GuitarML/SoundSketch/software/Pluto/pluto.cpp

#include "daisy_petal.h"
#include "daisysp.h"
#include "varSpeedLooper.h"
#include "soundsketch.h"
#include "reverbsc96.h"
#include "expressionHandler.h"

//
// This is a template for creating a pedal on the GuitarML Funbox_v1/Daisy Seed platform.
// You can start from here to fill out your effects processing and controls.
// Allows for Stereo In/Out, 6 knobs, 3 3-way switches,  2 SPST Footswitches, 2 LEDs.
//
// Keith Bloemer 5/20/2024
//

using namespace daisy;
using namespace daisysp;
using namespace soundsketch; 

// True bypass
GPIO audioBypassTrigger;
GPIO audioMuteTrigger;
bool m_audioBypass;
bool m_audioMute;

bool muteOn = false;
float muteOffTransitionTimeInSeconds = 0.02f;
int muteOffTransitionTimeInSamples;
int samplesTilMuteOff;

bool bypassOn = false;
float bypassToggleTransitionTimeInSeconds = 0.01f;
int bypassToggleTransitionTimeInSamples;
int samplesTilBypassToggle;


// Declare a local daisy_petal for hardware access
DaisyPetal hw;
Parameter levelA, modA, levelB, speedA, modB, speedB, expression;

// Looper Parameters
#define MAX_SIZE (96000 * 60) // 1 minute of floats at 96 khz
float DSY_SDRAM_BSS bufA[MAX_SIZE];
varSpeedLooper looperA;
Oscillator      led_oscA; // For pulsing the led when recording / paused playback
float           ledBrightnessA;
int             doubleTapCounterA;
bool            checkDoubleTapA;
bool            pausePlaybackA;
float           currentSpeedA;

float DSY_SDRAM_BSS bufB[MAX_SIZE];
varSpeedLooper looperB;
Oscillator      led_oscB; // For pulsing the led when recording / paused playback
float           ledBrightnessB;
int             doubleTapCounterB;
bool            checkDoubleTapB;
bool            pausePlaybackB;
float           currentSpeedB;

bool isPlaybackA, isPlaybackB;

// Reverb
ReverbSc96        verb;  // Minor change to ReverbSc to use 96kHz default samplerate

Tone toneA;       // Low Pass
ATone toneHPA;    // High Pass
Balance balA;     // Balance for volume correction in filtering

Tone toneB;       // Low Pass
ATone toneHPB;    // High Pass
Balance balB;     // Balance for volume correction in filtering

SmoothRandomGenerator smoothRandA;
SmoothRandomGenerator smoothRandB;

bool            bypass;

bool            pswitch1[2], pswitch2[2], pswitch3[2];
int             switch1[2], switch2[2], switch3[2];
int  switch1_action, switch2_action, switch3_action; // 0=left, 1=center, 2=right ; This is to aid midi control vs switch logic


Led led1, led2;


// Expression
ExpressionHandler expHandler;
bool expression_pressed;
float knobValues[6];
float pknobValues[6];


void SetAudioBypass(bool enabled) {
    m_audioBypass = enabled;
    audioBypassTrigger.Write(!m_audioBypass);
}

void SetAudioMute(bool enabled) {
    m_audioMute = enabled;
    audioMuteTrigger.Write(m_audioMute);
}

void InitTrueBypass(Pin relayPin, Pin mutePin) {
    // Init the HW Audio Bypass
    audioBypassTrigger.Init(relayPin, GPIO::Mode::OUTPUT);
    SetAudioBypass(true);

    // Init the HW Audio Mute
    audioMuteTrigger.Init(mutePin, GPIO::Mode::OUTPUT);
    SetAudioMute(false);

}

// Midi
bool midi_control[16]; // knobs 0-5, expression 6, switches 7-15 (three for each switch, first is true/false under midi control, second and third are switch values)

bool knobMoved(float old_value, float new_value)
{
    float tolerance = 0.005;
    if (new_value > (old_value + tolerance) || new_value < (old_value - tolerance)) {
        return true;
    } else {
        return false;
    }
}


void updateSwitch1() // left=, center=, right=
{
    if ((pswitch1[0] == true && !midi_control[7]) || ( midi_control[7] && midi_control[8] == true)) {  // left
        switch1_action = 0;

    } else if ((pswitch1[1] == true && !midi_control[7]) || ( midi_control[7] && midi_control[9] == true)) {  // right
        switch1_action = 2;

    } else {   // center
        switch1_action = 1;
    }      
}

void updateSwitch2() // left=, center=, right=
{
    if ((pswitch2[0] == true && !midi_control[10]) || ( midi_control[10] && midi_control[11] == true)) {  // left
        switch2_action = 0;
    } else if ((pswitch2[1] == true && !midi_control[10]) || ( midi_control[10] && midi_control[12] == true)) {  // right
        switch2_action = 2;

    } else {   // center
        switch2_action = 1;
    }    
}


void updateSwitch3() // left=, center=, right=
{
    if ((pswitch3[0] == true && !midi_control[13]) || ( midi_control[13] && midi_control[14] == true)) {  // left
        switch3_action = 0;
        looperA.SetMode(varSpeedLooper::Mode::NORMAL);
        looperB.SetMode(varSpeedLooper::Mode::NORMAL);

    } else if ((pswitch3[1] == true && !midi_control[13]) || ( midi_control[13] && midi_control[15] == true)) {  // right
        switch3_action = 2;
        looperA.SetMode(varSpeedLooper::Mode::FRIPPERTRONICS);
        looperB.SetMode(varSpeedLooper::Mode::FRIPPERTRONICS);

    } else {   // center
        switch3_action = 1;
        looperA.SetMode(varSpeedLooper::Mode::ONETIME_DUB);
        looperB.SetMode(varSpeedLooper::Mode::ONETIME_DUB);

    }    
}


void UpdateButtons()
{

    // LOOPER A //
    // Looper footswitch pressed (start/stop recording, doubletap to pause/unpause playback)
    if (hw.switches[Soundsketch::FOOTSWITCH_1].RisingEdge())
    {
        if (!pausePlaybackA) {
            looperA.TrigRecord();
            isPlaybackA = false;
            if (!looperA.Recording()) {  // Turn on LED if not recording and in playback
                led1.Set(1.0f);
                isPlaybackA = true;
            }
         
        }

        // Start or end double tap timer
        if (checkDoubleTapA) {
            // if second press comes before 1.0 seconds, pause playback
            if (doubleTapCounterA <= 1000) {
                if (looperA.Recording()) {  // Ensure looper is not recording when double tapped (in case it gets double tapped while recording)
                    looperA.TrigRecord();
                }
                pausePlaybackA = !pausePlaybackA;
                if (pausePlaybackA) {        // Blink LED if paused, otherwise set to triangle wave for pulsing while recording
                    led_oscA.SetWaveform(4); // WAVE_SIN = 0, WAVE_TRI = 1, WAVE_SAW = 2, WAVE_RAMP = 3, WAVE_SQUARE = 4
                } else {
                    led_oscA.SetWaveform(1); 
                }
                doubleTapCounterA = 0;    // reset double tap here also to prevent weird behaviour when triple clicked
                checkDoubleTapA = false;
                led1.Set(1.0f);
            }
        } else {
            checkDoubleTapA = true;
        }
    }

    if (checkDoubleTapA) {
        doubleTapCounterA += 1;          // Increment by 1 (48000 * 0.75)/blocksize = 1000   (blocksize is 48)
        if (doubleTapCounterA > 1000) {  // If timer goes beyond 1.0 seconds, stop double tap checking
            doubleTapCounterA = 0;
            checkDoubleTapA = false;
        }
    }

    // If switch1 is held, clear the looper and turn off LED
    if(hw.switches[Soundsketch::FOOTSWITCH_1].TimeHeldMs() >= 1000)
    {
        pausePlaybackA = false;
        led_oscA.SetWaveform(1); 
        looperA.Clear();
        led1.Set(0.0f);
    } 




    // LOOPER B //
    // Looper footswitch pressed (start/stop recording, doubletap to pause/unpause playback)


    if ((hw.switches[Soundsketch::FOOTSWITCH_2].RisingEdge()) || (hw.switches[Soundsketch::FOOTSWITCH_1].RisingEdge()) ) // TODO, verify this logic runs both loopers in the same way when in stereo mode
    {
        if (!pausePlaybackB) {
            looperB.TrigRecord();
            isPlaybackB = false;
            if (!looperB.Recording()) {  // Turn on LED if not recording and in playback
                led2.Set(1.0f);
                isPlaybackB = true;
            }
         
        }

        // Start or end double tap timer
        if (checkDoubleTapB) {
            // if second press comes before 1.0 seconds, pause playback
            if (doubleTapCounterB <= 1000) {
                if (looperB.Recording()) {  // Ensure looper is not recording when double tapped (in case it gets double tapped while recording)
                    looperB.TrigRecord();
                }
                pausePlaybackB = !pausePlaybackB;
                if (pausePlaybackB) {        // Blink LED if paused, otherwise set to triangle wave for pulsing while recording
                    led_oscB.SetWaveform(4); // WAVE_SIN = 0, WAVE_TRI = 1, WAVE_SAW = 2, WAVE_RAMP = 3, WAVE_SQUARE = 4
                } else {
                    led_oscB.SetWaveform(1); 
                }
                doubleTapCounterB = 0;    // reset double tap here also to prevent weird behaviour when triple clicked
                checkDoubleTapB = false;
                led2.Set(1.0f);
            }
        } else {
            checkDoubleTapB = true;
        }
    }

    if (checkDoubleTapB) {
        doubleTapCounterB += 1;          // Increment by 1 (48000 * 0.75)/blocksize = 1000   (blocksize is 48)
        if (doubleTapCounterB > 1000) {  // If timer goes beyond 1.0 seconds, stop double tap checking
            doubleTapCounterB = 0;
            checkDoubleTapB = false;
        }
    }

    // If switch2 is held, clear the looper and turn off LED
    if((hw.switches[Soundsketch::FOOTSWITCH_2].TimeHeldMs() >= 1000) || (hw.switches[Soundsketch::FOOTSWITCH_1].TimeHeldMs() >= 1000))
    {
        pausePlaybackB = false;
        led_oscB.SetWaveform(1); 
        looperB.Clear();
        led2.Set(0.0f);
    } 


}

/*
void setExpressionMode()  // Verify this only triggers when dipswitch changed
{
    if (pdip[2] == true) { 
        if (!expHandler.isExpressionSetMode())
            expHandler.ToggleExpressionSetMode();

        led1.Set(expHandler.returnLed1Brightness());  // Dim LEDs in expression set mode
        led2.Set(expHandler.returnLed2Brightness());  // Dim LEDs in expression set mode

        expression_pressed = true; 

    } else {       
        if (expHandler.isExpressionSetMode())
            expHandler.ToggleExpressionSetMode(); 

        led1.Set(isPlaybackA); // Set LED to on if loopers are in playback mode
        led2.Set(isPlaybackB);  
    }
}
*/

void UpdateSwitches()
{
    // Detect any changes in switch positions (3 On-Off-On switches and Dip switches)

    // 3-way Switch 1
    bool changed1 = false;
    for(int i=0; i<2; i++) {
        if (hw.switches[switch1[i]].Pressed() != pswitch1[i]) {
            pswitch1[i] = hw.switches[switch1[i]].Pressed();
            changed1 = true;
        }
    }
    if (changed1) {
        updateSwitch1();
        midi_control[7] = false;
    }

    // 3-way Switch 2
    bool changed2 = false;
    for(int i=0; i<2; i++) {
        if (hw.switches[switch2[i]].Pressed() != pswitch2[i]) {
            pswitch2[i] = hw.switches[switch2[i]].Pressed();
            changed2 = true;
        }
    }
    if (changed2) {
        updateSwitch2();
        midi_control[10] = false;
    }

    // 3-way Switch 3
    bool changed3 = false;
    for(int i=0; i<2; i++) {
        if (hw.switches[switch3[i]].Pressed() != pswitch3[i]) {
            pswitch3[i] = hw.switches[switch3[i]].Pressed();
            changed3 = true;
        }
    }
    if (changed3) {
        updateSwitch3();
        midi_control[13] = false;
    }

 /*
    // Dip switches
    for(int i=0; i<4; i++) {
        if (hw.switches[dip[i]].Pressed() != pdip[i]) {
            pdip[i] = hw.switches[dip[i]].Pressed();
            // Action for dipswitches handled in audio callback
            setExpressionMode();
        }
    }
*/

}



// This runs at a fixed rate, to prepare audio samples
static void AudioCallback(AudioHandle::InputBuffer  in,
                          AudioHandle::OutputBuffer out,
                          size_t                    size)
{
    //hw.ProcessAllControls();
    hw.ProcessAnalogControls();
    hw.ProcessDigitalControls();

    UpdateButtons();
    UpdateSwitches();

    // Knob, MIDI, and Expression Processing ////////////////////

    //float knobValues[6]; // moved to global
    float newExpressionValues[6];

    // Knob 1
    if (!midi_control[0])   // If not under midi control, use knob ADC
        pknobValues[0] = knobValues[0] = levelA.Process();
    else if (knobMoved(pknobValues[0], levelA.Process()))  // If midi controlled, watch for knob movement to end Midi control
        midi_control[0] = false;

    // Knob 2
    if (!midi_control[1])   // If not under midi control, use knob ADC
        pknobValues[1] = knobValues[1] = modA.Process();
    else if (knobMoved(pknobValues[1], modA.Process()))  // If midi controlled, watch for knob movement to end Midi control
        midi_control[1] = false;

    // Knob 3
    if (!midi_control[2])   // If not under midi control, use knob ADC
        pknobValues[2] = knobValues[2] = levelB.Process();
    else if (knobMoved(pknobValues[2], levelB.Process()))  // If midi controlled, watch for knob movement to end Midi control
        midi_control[2] = false;

    // Knob 4
    if (!midi_control[3])   // If not under midi control, use knob ADC
        pknobValues[3] = knobValues[3] = speedA.Process();
    else if (knobMoved(pknobValues[3], speedA.Process()))  // If midi controlled, watch for knob movement to end Midi control
        midi_control[3] = false;
    

    // Knob 5
    if (!midi_control[4])   // If not under midi control, use knob ADC
        pknobValues[4] = knobValues[4] = modB.Process();
    else if (knobMoved(pknobValues[4], modB.Process()))  // If midi controlled, watch for knob movement to end Midi control
        midi_control[4] = false;
    

    // Knob 6
    if (!midi_control[5])   // If not under midi control, use knob ADC
        pknobValues[5] = knobValues[5] = speedB.Process();
    else if (knobMoved(pknobValues[5], speedB.Process()))  // If midi controlled, watch for knob movement to end Midi control
        midi_control[5] = false;
    


    // Expression  // TODO Not working, need to fix logic
    if (!midi_control[6])   // If not under midi control, use expression pedal input
        pknobValues[6] = expression.Process();
     else if (knobMoved(pknobValues[6], expression.Process()))  // If midi controlled, watch for knob movement to end Midi control
        midi_control[6] = false;
    

    //float vexpression = expression.Process(); // 0 is heel (up), 1 is toe (down)
    //expHandler.Process(vexpression, knobValues, newExpressionValues);

    expHandler.Process(pknobValues[6], knobValues, newExpressionValues);


    // If in expression set mode, set LEDS accordingly
    if (expHandler.isExpressionSetMode()) {
        led1.Set(expHandler.returnLed1Brightness());
        led2.Set(expHandler.returnLed2Brightness());
    }
  

    float vlevelA = newExpressionValues[0];
    float vmodA = newExpressionValues[1];
    float vlevelB = newExpressionValues[2];

    float vspeedA = newExpressionValues[3];
    float vmodB = newExpressionValues[4];
    float vspeedB = newExpressionValues[5];

    // Handle Knob Changes Here


    // LOOPER A
    float speed_inputA = 0.0;
    float speed_inputAabs = 0.0;


    // If switch1 in left position and not under midi control, or under midi control and set accordingly
    if (switch1_action == 0) { // Switch1 left = smooth

        if (vspeedA <= 0.5) {
            speed_inputA = vspeedA * 6.0 - 2.0; // maps 0 to 0.5 control to -2x to 1x speed

        } else {
            speed_inputA = vspeedA * 2.0;  // maps 0.5 to 1.0 control to 1x to 2x speed

        }


    } else if (switch1_action == 2) { // Switch1 right = random TODO

    } else {                        // Switch1 center = stepped  // TODO Verify that I don't need some kind of midi check here
        if (vspeedA < 0.05) {
            speed_inputA = -2.0;
        } else if (vspeedA >= 0.05 && vspeedA <= 0.15) {
            speed_inputA = -1.5;
        } else if (vspeedA >= 0.15 && vspeedA <= 0.25) {
            speed_inputA = -1.0;
        } else if (vspeedA >= 0.25 && vspeedA <= 0.35) {
            speed_inputA = -0.5;
        } else if (vspeedA >= 0.35 && vspeedA <= 0.45) {
            speed_inputA = 0.5;
        } else if (vspeedA >= 0.45 && vspeedA <= 0.55) {  // Noon is 1x speed
            speed_inputA = 1.0;
        } else if (vspeedA >= 0.55 && vspeedA <= 0.7) {
            speed_inputA = 1.5;
        } else if (vspeedA >= 0.7 && vspeedA <= 0.8) {
            speed_inputA = 2.0;
        } else if (vspeedA >= 0.8 && vspeedA <= 0.9) {
            speed_inputA = 2.5;
        } else {
            speed_inputA = 3.0;
        }

        if (speed_inputA < 0.0) {
            looperA.SetReverse(true);
        } else {
            looperA.SetReverse(false);
        }
        speed_inputAabs = abs(speed_inputA);

        looperA.SetIncrementSize(speed_inputAabs);
    }



    // LOOPER B
    float speed_inputB = 0.0;
    float speed_inputBabs = 0.0;

    // TODO At some point combine the logic of using pswitch1 for both loopers
    if (switch1_action == 0) { // Switch3 left = smooth
        if (vspeedB <= 0.5) {
            speed_inputB = vspeedB * 6.0 - 2.0; // maps 0 to 0.5 control to -2x to 1x speed

        } else {
            speed_inputB = vspeedB * 2.0;  // maps 0.5 to 1.0 control to 1x to 2x speed

        }

    } else if (switch1_action == 2) { // Switch3 right = random TODO

    } else {                        // Switch3 center = stepped
        if (vspeedB < 0.05) {
            speed_inputB = -2.0;
        } else if (vspeedB >= 0.05 && vspeedB <= 0.15) {
            speed_inputB = -1.5;
        } else if (vspeedB >= 0.15 && vspeedB <= 0.25) {
            speed_inputB = -1.0;
        } else if (vspeedB >= 0.25 && vspeedB <= 0.35) {
            speed_inputB = -0.5;
        } else if (vspeedB >= 0.35 && vspeedB <= 0.45) {
            speed_inputB = 0.5;
        } else if (vspeedB >= 0.45 && vspeedB <= 0.55) {  // Noon is 1x speed
            speed_inputB = 1.0;
        } else if (vspeedB >= 0.55 && vspeedB <= 0.7) {
            speed_inputB = 1.5;
        } else if (vspeedB >= 0.7 && vspeedB <= 0.8) {
            speed_inputB = 2.0;
        } else if (vspeedB >= 0.8 && vspeedB <= 0.9) {
            speed_inputB = 2.5;
        } else {
            speed_inputB = 3.0;
        }

        if (speed_inputB < 0.0) {
            looperB.SetReverse(true);
        } else {
            looperB.SetReverse(false);
        }
        speed_inputBabs = abs(speed_inputB);

        looperB.SetIncrementSize(speed_inputBabs);
    }





    // EFFECTS //
    if (switch2_action == 0) { // Center switch left

        smoothRandA.SetFreq(vmodA*4);
        smoothRandB.SetFreq(vmodB*4);
        

    } else if (switch2_action == 2) { // Center switch right
        float vReverbTime = vmodA;
        if (vReverbTime < 0.01) { // if knob < 1%, set reverb to 0
            verb.SetFeedback(0.0);
        } else if (vReverbTime >= 0.01 && vReverbTime <= 0.1) {
            verb.SetFeedback(vReverbTime * 6.4 ); // Reverb time range 0.0 to 0.6 for 1% to 10% knob turn (smooth ramping to useful reverb time values, i.e. 0.6 to 1)
        } else {
            verb.SetFeedback(vReverbTime * 0.4 + 0.6); // Reverb time range 0.6 to 1.0
        }

        float invertedFreq = 1.0 - vmodB; // Invert the damping param so that knob left is less dampening, knob right is more dampening
        invertedFreq = invertedFreq * invertedFreq; // also square it for exponential taper (more control over lower frequencies)
        verb.SetLpFreq(600.0 + invertedFreq * (16000.0 - 600.0));

    } else { // Center switch center

       // TODO Need to do CUBE taper for this filter control
       float vfilterA = vmodA;
        // Set Filter Controls
        if (vfilterA <= 0.5) {
            float filter_valueA = (vfilterA * vfilterA * vfilterA * 39800.0f) + 80.0f;
            toneA.SetFreq(filter_valueA);
        } else {
            vfilterA = vfilterA - 0.5;
            float filter_valueA = (vfilterA * vfilterA) * 500.0f + 40.0f;
            toneHPA.SetFreq(filter_valueA);
        }

        float vfilterB = vmodB;
        // Set Filter Controls
        if (vfilterB <= 0.5) {
            float filter_valueB = (vfilterB * vfilterB * vfilterB *  39800.0f) + 80.0f;
            toneB.SetFreq(filter_valueB);
        } else {
            vfilterB = vfilterB - 0.5;
            float filter_valueB = (vfilterB  * vfilterB) * 500.0f + 40.0f;
            toneHPB.SetFreq(filter_valueB);
        }
    }

    float inL, inR;
    float sendl, sendr, wetl, wetr;

    for(size_t i = 0; i < size; i++)
    {

        // Handle true bypass relay
        if (samplesTilMuteOff > 0) {
            samplesTilMuteOff -= 1;
            if (samplesTilMuteOff < 1) {
                SetAudioMute(false);
            }
        }

        if (samplesTilBypassToggle > 0) {
            samplesTilBypassToggle -= 1;
            if (samplesTilBypassToggle < 1) {
                SetAudioBypass(bypass);
            }
        }

        ledBrightnessA = led_oscA.Process();
        ledBrightnessB = led_oscB.Process();

        // Handle smooth speed knob transitions
        if (switch1_action == 0) { // Switch1 left = smooth
            // Smooth out Looper A transitions
            fonepole(currentSpeedA, speed_inputA, .00006f); 

            if (currentSpeedA < 0.0) {
                looperA.SetReverse(true);
            } else {
                looperA.SetReverse(false);
            }
            speed_inputAabs = abs(currentSpeedA);
            looperA.SetIncrementSize(speed_inputAabs);


            // Smooth out Looper B transitions
            fonepole(currentSpeedB, speed_inputB, .00006f);  

            if (currentSpeedB < 0.0) {
                looperB.SetReverse(true);
            } else {
                looperB.SetReverse(false);
            }
            speed_inputBabs = abs(currentSpeedB);
            looperB.SetIncrementSize(speed_inputBabs);

        } 

        if (switch2_action == 0) {    // Stability
            // Set Stablility of Loops
            looperA.SetIncrementSize(speed_inputAabs + smoothRandA.Process() * vmodA * 0.05);
            looperB.SetIncrementSize(speed_inputBabs + smoothRandB.Process() * vmodB * 0.05);
        }


        // Process your signal here

        inL = in[0][i];
        inR = in[0][i];


        /// Process Looper A // 
        float loop_outA = 0.0;
        if (!pausePlaybackA) {
            loop_outA = looperA.Process(inL) * vlevelA * 2.0;
        }

        /// Process Looper B // 
        float loop_outB = 0.0;
        if (!pausePlaybackB) {
            loop_outB = looperB.Process(inR) * vlevelB * 2.0;
        }

        wetl = wetr = 0.0;

        if (switch2_action == 2) {  // Reverb
            sendl = loop_outA;
            sendr = loop_outB;
            verb.Process(sendl, sendr, &wetl, &wetr);

        } else if (switch2_action == 1) {                 // Filter
            // Process Tone
            float filter_inA =  loop_outA;
            float filter_outA;
            
            if (vmodA <= 0.5) {
                filter_outA = toneA.Process(filter_inA);
                loop_outA = balA.Process(filter_outA, filter_inA);

            } else {
                filter_outA = toneHPA.Process(filter_inA);
                loop_outA = balA.Process(filter_outA, filter_inA);
            }

            // Process Tone
            float filter_inB =  loop_outB;
            float filter_outB;
            
            if (vmodB <= 0.5) {
                filter_outB = toneB.Process(filter_inB);
                loop_outB = balB.Process(filter_outB, filter_inB);

            } else {
                filter_outB = toneHPA.Process(filter_inB);
                loop_outB = balA.Process(filter_outB, filter_inB);
            }

        }


        out[0][i] = inL + loop_outA + loop_outB + wetl;
        out[1][i] = inR + loop_outA + loop_outB + wetr;
        
     
    }

    // Handle Pulsing LEDs
    if (looperA.Recording()) {
        led1.Set(ledBrightnessA * 0.5 + 0.5);       // Pulse the LED when recording
    } 

    if (pausePlaybackA) {
        led1.Set(ledBrightnessA * 2.0);             // Blink the LED when paused
    }


    if (looperB.Recording()) {
        led2.Set(ledBrightnessB * 0.5 + 0.5);       // Pulse the LED when recording
    } 
    if (pausePlaybackB) {
        led2.Set(ledBrightnessB * 2.0);             // Blink the LED when paused
    }
   

    led1.Update();
    led2.Update();
}

// Typical Switch case for Message Type.
void HandleMidiMessage(MidiEvent m)
{
    switch(m.type)
    {
        case NoteOn:
        {
 
            led2.Set(1.0); // TODO Simple test to see if midi note is detected
            led2.Update();
            NoteOnEvent p = m.AsNoteOn();
            // This is to avoid Max/MSP Note outs for now..
            if(m.data[1] != 0)
            {
                p = m.AsNoteOn();
                // Do stuff with the midi Note/Velocity info here
                //osc.SetFreq(mtof(p.note));
                //osc.SetAmp((p.velocity / 127.0f));
            }
        }
        break;
        case ControlChange:
        {

            ControlChangeEvent p = m.AsControlChange();
            switch(p.control_number)
            {
                case 14:
                    midi_control[0] = true;
                    knobValues[0] = ((float)p.value / 127.0f);
                    break;
                case 15:
                    midi_control[1] = true;
                    knobValues[1] = ((float)p.value / 127.0f);
                    break;
                case 16:
                    midi_control[2] = true;
                    knobValues[2] = ((float)p.value / 127.0f);
                    break;
                case 17:
                    midi_control[3] = true;
                    knobValues[3] = ((float)p.value / 127.0f);
                    break;
                case 18:
                    midi_control[4] = true;
                    knobValues[4] = ((float)p.value / 127.0f);
                    break;
                case 19:
                    midi_control[5] = true;
                    knobValues[5] = ((float)p.value / 127.0f);
                    break;

                case 21:  // TODO Switch1 not working over Midi, fix
                    midi_control[7] = true;
                    if (p.value == 0 || p.value == 1) {
                        midi_control[8] = true;
                        midi_control[9] = false;
                    } else if (p.value == 2) {
                        midi_control[8] = false;
                        midi_control[9] = false;
                    } else {
                        midi_control[8] = false;
                        midi_control[9] = true;
                    }
                    updateSwitch1();
                    break;

                case 22:
                    midi_control[10] = true;
                    if (p.value == 0 || p.value == 1) {
                        midi_control[11] = true;
                        midi_control[12] = false;
                    } else if (p.value == 2) {
                        midi_control[11] = false;
                        midi_control[12] = false;
                    } else {
                        midi_control[11] = false;
                        midi_control[12] = true;
                    }
                    updateSwitch2();
                    break;

                case 23:
                    midi_control[13] = true;
                    if (p.value == 0 || p.value == 1) {
                        midi_control[14] = true;
                        midi_control[15] = false;
                    } else if (p.value == 2) {
                        midi_control[14] = false;
                        midi_control[15] = false;
                    } else {
                        midi_control[14] = false;
                        midi_control[15] = true;
                    }
                    updateSwitch3();
                    break;


                case 100:
                    midi_control[6] = true;
                    knobValues[6] = ((float)p.value / 127.0f);
                    break;

                default: break;
            }
            break;
        }
        default: break;
    }
}


int main(void)
{
    float samplerate;

    hw.Init(true); 
    
    hw.SetAudioSampleRate(SaiHandle::Config::SampleRate::SAI_96KHZ);  // Test raising the samplerate to have higher fidelity at slower playback speeds
                                                                        // ReverbSC doesn't work running at 96kHz, TODO look into getting this working
    samplerate = hw.AudioSampleRate();  

    hw.SetAudioBlockSize(48);

    switch1[0]= Soundsketch::SWITCH_1_UP;
    switch1[1]= Soundsketch::SWITCH_1_DOWN;
    switch2[0]= Soundsketch::SWITCH_2_UP;
    switch2[1]= Soundsketch::SWITCH_2_DOWN;
    switch3[0]= Soundsketch::SWITCH_3_UP;
    switch3[1]= Soundsketch::SWITCH_3_DOWN;

    pswitch1[0]= false;
    pswitch1[1]= false;
    pswitch2[0]= false;
    pswitch2[1]= false;
    pswitch3[0]= false;
    pswitch3[1]= false;
    //switch1_action = switch2_action = switch3_action = 0;

    // True Bypass
    bypassToggleTransitionTimeInSamples = samplerate * bypassToggleTransitionTimeInSeconds;
    muteOffTransitionTimeInSamples = samplerate * muteOffTransitionTimeInSeconds;
    InitTrueBypass(seed::D1, seed::D12); // (relaypin=D1, mutepin=D12)

    samplesTilMuteOff = 0;
    samplesTilBypassToggle = 0;

    levelA.Init(hw.knob[Soundsketch::KNOB_1], 0.0f, 1.0f, Parameter::LINEAR);
    modA.Init(hw.knob[Soundsketch::KNOB_2], 0.0f, 1.0f, Parameter::LINEAR);
    levelB.Init(hw.knob[Soundsketch::KNOB_3], 0.0f, 1.0f, Parameter::LINEAR); 
    speedA.Init(hw.knob[Soundsketch::KNOB_4], 0.0f, 1.0f, Parameter::LINEAR);
    modB.Init(hw.knob[Soundsketch::KNOB_5], 0.0f, 1.0f, Parameter::LINEAR);
    speedB.Init(hw.knob[Soundsketch::KNOB_6], 0.0f, 1.0f, Parameter::LINEAR); 
    expression.Init(hw.expression, 0.0f, 1.0f, Parameter::LINEAR); 


    looperA.Init(bufA, MAX_SIZE);
    looperA.SetMode(varSpeedLooper::Mode::NORMAL);
    led_oscA.Init(samplerate);
    led_oscA.SetFreq(1.0);
    led_oscA.SetWaveform(1); // WAVE_SIN = 0, WAVE_TRI = 1, WAVE_SAW = 2, WAVE_RAMP = 3, WAVE_SQUARE = 4
    ledBrightnessA = 0.0;
    pausePlaybackA = false;
    currentSpeedA = 1.0;

    led_oscA.Init(samplerate);
    led_oscA.SetFreq(1.5);
    led_oscA.SetWaveform(1);



    looperB.Init(bufB, MAX_SIZE);
    looperB.SetMode(varSpeedLooper::Mode::NORMAL);
    led_oscB.Init(samplerate);
    led_oscB.SetFreq(1.0);
    led_oscB.SetWaveform(1); // WAVE_SIN = 0, WAVE_TRI = 1, WAVE_SAW = 2, WAVE_RAMP = 3, WAVE_SQUARE = 4
    ledBrightnessB = 0.0;
    pausePlaybackB = false;
    currentSpeedB = 1.0;
    isPlaybackA = isPlaybackB = false;

    led_oscB.Init(samplerate);
    led_oscB.SetFreq(1.5);
    led_oscB.SetWaveform(1);

    verb.Init(samplerate); 

    toneA.Init(samplerate);
    toneHPA.Init(samplerate);
    balA.Init(samplerate);

    toneB.Init(samplerate);
    toneHPB.Init(samplerate);
    balB.Init(samplerate);


    smoothRandA.Init(samplerate);
    smoothRandB.Init(samplerate);
    

    // Expression
    expHandler.Init(6);
    expression_pressed = false;

    // Midi
    for( int i = 0; i < 16; ++i ) 
        midi_control[i] = false;  // Is this needed? or does it default to false
    // index for midi_control: 0-5 knobs, 6 expression, 7-9 switch1, 10-12 switch2, 13-15 switch 3


    // Init the LEDs and set activate bypass
    led1.Init(hw.seed.GetPin(Soundsketch::LED_1),false);
    led1.Update();
    bypass = true;

    led2.Init(hw.seed.GetPin(Soundsketch::LED_2),false);
    led2.Update();

    hw.InitMidi();
    hw.midi.StartReceive();

    hw.StartAdc();
    hw.StartAudio(AudioCallback);
    while(1)
    {
        hw.midi.Listen();
        // Handle MIDI Events
        while(hw.midi.HasEvents())
        {
            HandleMidiMessage(hw.midi.PopEvent());
        }

    }
}
