GuitarML/SoundSketch/software/Mercury/model_data_nam.h

struct modelDataNam {
  std::vector<float> weights; 
};

// ADD YOUR MODEL IDENTIFIER HERE ////////////////////////////////// < -------------------
modelDataNam NamModel1; 
modelDataNam NamModel2; 
modelDataNam NamModel3; 
modelDataNam NamModel4; 
modelDataNam NamModel5; 
modelDataNam NamModel6; 
modelDataNam NamModel7; 
modelDataNam NamModel8; 
modelDataNam NamModel9; 

/////////////////////////////////////////////////////////////////

std::vector<modelDataNam> model_collection_nam;

/*========================================================================*/

void setupWeightsNam() {





// COPY AND PASTE YOUR MODEL WEIGHTS BELOW (After converting .json to .h file) ////////////////////////////////// < -------------------
//   ADD AND REMOVE MODELS AS DESIRED (CAN HOLD AROUND 15-16 MODELS IN FLASH MEMORY)



  //========================================================================
// NAM Pico Models 
/*
{"version": "0.5.4", "metadata": {"date": {"year": 2024, "month": 12, "day": 28, "hour": 10, "minute": 21, "second": 12}, "loudness": -12.713208198547363, "gain": 0.6453793642123751}, "architecture": "WaveNet", "config": {"layers": [{"input_size": 1, "condition_size": 1, "head_size": 2, "channels": 2, "kernel_size": 3, "dilations": [1, 2, 4, 8, 16, 32, 64], "activation": "Tanh", "gated": false, "head_bias": false}, {"input_size": 2, "condition_size": 1, "head_size": 1, "channels": 2, "kernel_size": 3, "dilations": [128, 256, 512, 1, 2, 4, 8, 16, 32, 64, 128, 256, 512], "activation": "Tanh", "gated": false, "head_bias": true}], "head": null, "head_scale": 0.02},
*/

  // Matchless loss= 0.012  Epochs=300
  NamModel1.weights =  {-1.0522884130477905, 1.195845603942871, -0.5518407225608826, -0.7661945819854736, -0.03622770309448242, -0.1075611561536789, 0.07998702675104141, 0.17400622367858887, 0.13933351635932922, -0.005570037756115198, -0.03101075068116188, -0.18490272760391235, -0.18909011781215668, -0.17499856650829315, -0.29526469111442566, 0.058663688600063324, -0.03600570932030678, 0.12594614923000336, -0.44604727625846863, -0.03029322251677513, 0.12411181628704071, 0.4513852000236511, -0.14389470219612122, 0.18362830579280853, -0.2561951279640198, -0.07560718059539795, 0.21923302114009857, -0.4908706843852997, -0.48271575570106506, 0.746678352355957, -0.17638328671455383, 0.46193113923072815, -0.9297204613685608, -0.14872944355010986, -0.3476191759109497, 0.34131816029548645, -0.10461179912090302, 0.11907011270523071, 0.7986811995506287, 0.21213123202323914, 0.0009842534782364964, 0.2777601480484009, 0.00412560673430562, -0.2700638175010681, -0.5428489446640015, -0.14008310437202454, 0.2149878591299057, 0.4233935475349426, -0.08873198926448822, 0.015780411660671234, 0.4918768107891083, 0.31576067209243774, 0.05965155363082886, 0.03482469543814659, 0.18896672129631042, -0.0439361110329628, 0.10933125019073486, -0.560279130935669, -0.7729668021202087, -0.5656353235244751, -0.13570427894592285, -0.5890295505523682, 0.20838765799999237, 0.47209838032722473, 0.4683716595172882, 0.2606602609157562, -0.1885690838098526, -0.07050450891256332, 0.6914271116256714, 0.39520952105522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

  // Twin Reverb 0.03 Epochs=100
  NamModel2.weights =  {0.20864363014698029, 0.8024476766586304, -0.5351406335830688, -0.6766833066940308, -0.34967008233070374, -0.33313119411468506, -0.3266916573047638, 0.45169398188591003, 0.04592067748308182, -0.2145940661430359, -0.3234618306159973, -0.12928034365177155, 0.006090836133807898, -0.41874170303344727, -0.19540219008922577, 0.3014377951622009, -0.13174526393413544, 0.20819781720638275, -0.05995114520192146, 0.07647346705198288, 0.22077742218971252, 0.6153808236122131, -0.2509903609752655, 0.10627347975969315, -0.40312454104423523, -0.18083126842975616, 0.14420807361602783, -0.6355199217796326, 0.009535601362586021, -0.06358958035707474, 0.07137507945299149, 0.25922438502311707, -0.5471367835998535, 0.22598060965538025, -0.18669572472572327, 0.09104667603969574, -0.4943769872188568, 0.22829240560531616, 0.47123658657073975, -0.21968361735343933, 0.1364227533340454, -0.1746380627155304, 0.21890497207641602, -0.16407759487628937, -0.45725709199905396, 0.31019991636276245, 0.10639270395040512, 0.4335137903690338, -0.5429285764694214, -0.12037386000156403, 0.4254966378211975, -0.16419951617717743, 0.1343764066696167, 0.040155403316020966, 0.28186115622520447, -0.13638544082641602, -0.0901947170495987, -0.41048893332481384, -0.3539474904537201, -0.08362623304128647, 0.27706611156463623, 0.23463213443756104, -0.15649837255477905, 0.15050551295280457, 0.6457645893096924, -0.012075352482497692, -0.18517644703388214, -0.4029207229614258, 0.5426814556121826, 0.42987903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

  // Mesa Boogie Mark III red stripe (-87) ( nano / standard ) crunch
  NamModel4.weights =  {-0.42343246936798096, 0.37794575095176697, -1.0479851961135864, -1.084951400756836, 0.35355788469314575, 0.3534632921218872, -0.002321320353075862, -0.23648600280284882, -0.3001570701599121, 0.08283548802137375, 0.3419627249240875, 0.21857069432735443, -0.26315999031066895, 0.24479854106903076, 0.15169012546539307, 0.017826836556196213, 0.1296870857477188, 0.0684669092297554, -0.27995556592941284, -0.1840093433856964, 0.17625442147254944, 0.2881954610347748, -0.04944377392530441, 0.14138057827949524, -0.10051002353429794, 0.04558810964226723, 0.1789880394935608, -0.32444992661476135, -0.25065043568611145, 0.10053152590990067, 0.27357110381126404, 0.2893611788749695, -0.32168352603912354, -0.48902979493141174, -0.22297485172748566, -0.09879575669765472, 0.22654737532138824, 0.20697128772735596, 0.28608328104019165, 0.5200234055519104, -0.5499699115753174, -0.12632176280021667, 0.15317736566066742, 0.25572896003723145, -0.30977943539619446, -0.35958316922187805, -0.3103927969932556, 0.25053098797798157, 0.03181106969714165, -0.5255736708641052, 0.25108277797698975, 0.43923914432525635, -0.004536432679742575, 0.06310444325208664, 0.7900881767272949, -0.13600321114063263, 0.1672089844942093, -0.7336614727973938, -1.0910792350769043, -0.6826286315917969, -0.0823131799697876, 0.2668956518173218, 0.04791729152202606, 0.6428545117378235, 0.18911495804786682, 0.11191105842590332, 0.12080216407775879, 0.3526844084262848, 0.2202235907316208, 0.5125946402549744, -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
    
  // Solar chug pre tonehunt
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
